Krupson/Scoreboard/3d/stls/Scoreboard_Tablica wyników_Szablon początek bottom.stl

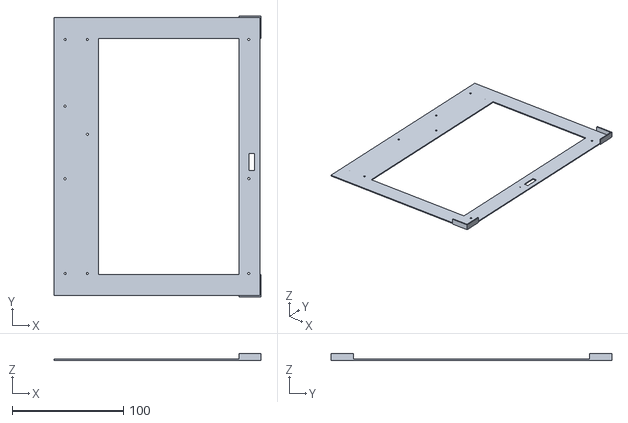
[picture p12: CAD file, 2026-05-05]
3d/stls/Scoreboard_Tablica wyników_Szablon początek bottom.stl
186.3 x 252.6 x 6.00
